tjhowse/OpenJoystick/modcon/modcon.scad

// Wall thickness
wt = 3;
// Pre-drill hole/groove depth
pd_groove_z = 1;
pd_groove_x = 1;
pd_hole_r = 1;
pd_hole_z = pd_groove_z;
// Grid spacing for the straight pre-drill grooves
pd_grid_xy = 5;
// Leave this much room around the edge without pre-drill grooves/holes.
pd_grid_clearance = 10;
// A list of radii for the circular pre-drill grooves
circles_r = [10, 20, 30];
// Overall width/height
unit_xy = 80;
unit_z = 50;
lid_screw_offset_x = wt*2;
lid_screw_shaft_r = 1.5;
lid_recess_grace = 0.4; // How much to shink the recessed part of the lid so it sockets into the base.

join_pin_x = 3*wt;
join_pin_z = join_pin_x;

// join_pin goes through the holes in the sides of the bases to lock them together.
module join_pin() {
    cube([join_pin_x+2*wt, wt, join_pin_z]);
    translate([wt,wt,0]) cube([join_pin_x, 2*wt, join_pin_z]);
    translate([wt*2,wt*3,0]) cube([wt, wt, join_pin_z]);
    translate([wt*2, wt*3,0]) rotate([0,0,90]) pin_barb();
    translate([wt*4, wt*4,0]) rotate([0,0,180]) pin_barb();

}

// join_pin_clip latches over the end of the join_pin to lock it into place
module join_pin_clip() {
    clip_scale = 1.1;
    scale([clip_scale, clip_scale, 1]) difference(){
        cube([join_pin_x+2*wt, 2*wt, join_pin_z]);
        translate([join_pin_x+2*wt, wt*5,0]) rotate([0,0,180]) join_pin();
    }
}

// pin_barb is a part of the join_pin
module pin_barb() {
    translate([wt/2, wt/2, join_pin_z/2]) difference() {
        cube([wt, wt, join_pin_z], center=true);
        rotate([0,0,45]) translate([-50,0,-join_pin_z/2]) cube([100,10,join_pin_z]);
    }
}

// spring_pin is a variant on the join_pin that uses a barbed spring arrangement
// rather than the two-piece version.
module spring_pin() {
    cube([join_pin_x+2*wt, wt, join_pin_z]);
    translate([wt,wt,0]) cube([wt/2, wt*3, join_pin_z]);
    translate([3.5*wt,wt,0]) cube([wt/2, wt*3, join_pin_z]);
    translate([0,3*wt,0]) rotate([0,0,0]) #pin_barb();
    translate([4*wt,4*wt,0]) rotate([0,0,270]) #pin_barb();
}
// spring_pin();

// join_pin_holes is for chopping the locking holes in the sides of the base
module join_pin_holes() {
    ratio = 4;
    translate([unit_xy/ratio,0,0]) cube([join_pin_z, 200, join_pin_x], center=true);
    translate([-unit_xy/ratio,0,0]) cube([join_pin_z, 200, join_pin_x], center=true);
    rotate([0,0,90]) {
        translate([unit_xy/ratio,0,0]) cube([join_pin_z, 200, join_pin_x], center=true);
        translate([-unit_xy/ratio,0,0]) cube([join_pin_z, 200, join_pin_x], center=true);
    }
}

// grid_screw is an M3x20 cup head bolt by default
module lid_screw() {
    head_r = 3;
    bolt_head_protrusion_z = 3;
    head_z = 3-bolt_head_protrusion_z;
    shaft_r = lid_screw_shaft_r;
    shaft_z = 20;
    cylinder(r=head_r, h=head_z);
    translate([0,0,head_z]) cylinder(r=shaft_r, h=shaft_z, $fn=10);
}

// base_screw_post is one of the corner screw posts for the base.
module base_screw_post() {
    difference() {
        cylinder(r=lid_screw_shaft_r+wt, h=unit_z-wt*2);
        cylinder(r=lid_screw_shaft_r, h=unit_z-wt*2, $fn=10);
    }
}

// base_screw_posts are the four posts in the corners inside the
// base. These posts provide the holes for screws that hold the lid
// on, and also add rigidity to the base by reinforcing the corners.
module base_screw_posts() {
    intersection() {
        cube([unit_xy, unit_xy, unit_z-wt/2]);
        union() {
            translate([lid_screw_offset_x, lid_screw_offset_x, wt]) base_screw_post();
            translate([unit_xy-lid_screw_offset_x, lid_screw_offset_x, wt]) base_screw_post();
            translate([unit_xy-lid_screw_offset_x, unit_xy-lid_screw_offset_x, wt]) base_screw_post();
            translate([lid_screw_offset_x, unit_xy-lid_screw_offset_x, wt]) base_screw_post();
        }
    }
}

// base is the body of the module. Basically everything except the lid.
module base() {
    difference () {
        cube([unit_xy, unit_xy, unit_z-wt/2]);
        translate([wt, wt, wt]) cube([unit_xy-2*wt, unit_xy-2*wt, unit_z]);
        translate([unit_xy/2, unit_xy/2, unit_z/2]) join_pin_holes();
    }
    base_screw_posts();
}

module lid_whole() {
    cube([unit_xy, unit_xy, wt/2]);
    translate([wt+lid_recess_grace/2,wt+lid_recess_grace/2,wt/2])
        cube([unit_xy-wt*2-lid_recess_grace, unit_xy-wt*2-lid_recess_grace, wt/2]);
}

// lid_lines is half of the straight lines in the underside of the lid
module lid_lines() {
    for (x = [pd_grid_clearance:pd_grid_xy:unit_xy-pd_grid_clearance]) {
        translate([x-pd_groove_x/2, pd_grid_clearance, 0]) cube([pd_groove_x, unit_xy-2*pd_grid_clearance, 10]);
    }
}

// lid_grid is subtracted from the lid to provide the grid
// lines to assist with drilling accurately spaced holes or
// punching out neat sections. Currently unused.
module lid_grid() {
    // lid_lines();
    // translate([unit_xy, 0, 0]) rotate([0,0,90]) lid_lines();
    for (x = [pd_grid_clearance:pd_grid_xy:unit_xy-pd_grid_clearance]) {
        for (y = [pd_grid_clearance:pd_grid_xy:unit_xy-pd_grid_clearance]) {
            translate([x, y, 0]) cylinder(r=pd_hole_r, h=10, $fn=10);
        }
    }
}

// lid_circles is subtracted from the underside of the lid
// to make it easier to punch out portions of the lid to mount
// stuff.
module lid_circles() {
    for (r = circles_r) {
        difference() {
            cylinder(r=r+pd_groove_x/2, h=10);
            cylinder(r=r-pd_groove_x/2, h=10);
        }
    }
}

// lid is the lid of a module. The grooves argument lets you turn off the grooves for improved
// rendering speed.
module lid(grooves = 1) {
    difference() {
        lid_whole();
        lsox = lid_screw_offset_x;
        translate([lsox, lsox,0]) lid_screw();
        translate([unit_xy-lsox, lsox,0]) lid_screw();
        translate([unit_xy-lsox, unit_xy-lsox,0]) lid_screw();
        translate([lsox, unit_xy-lsox,0]) lid_screw();

        if (grooves) {
            translate([unit_xy/2, unit_xy/2, wt-pd_groove_z]) lid_circles();
            translate([0, 0, wt-pd_hole_z]) lid_grid();
        }
    }
}

// lid_HW997 is a variant of the lid with the holes to mount the HW0000997 joystick
// already formed.
module lid_HW997(grooves = 1) {
    $fn=20;
    HD997_hole_r = 41/2;
    HD997_screw_spacing_xy = 32.5/2;
    HD997_screw_hole_r = 2.5/2;
    difference() {
        lid(0);
        translate([unit_xy/2, unit_xy/2,0]) {
            cylinder(r=HD997_hole_r, h=100);
            translate([HD997_screw_spacing_xy,HD997_screw_spacing_xy,0]) cylinder(r=HD997_screw_hole_r, h=100);
            translate([-HD997_screw_spacing_xy,HD997_screw_spacing_xy,0]) cylinder(r=HD997_screw_hole_r, h=100);
            translate([HD997_screw_spacing_xy,-HD997_screw_spacing_xy,0]) cylinder(r=HD997_screw_hole_r, h=100);
            translate([-HD997_screw_spacing_xy,-HD997_screw_spacing_xy,0]) cylinder(r=HD997_screw_hole_r, h=100);
        }

    }
}

10a_switch_r = 6;
10a_switch_x = 20;
10a_switch_clearance_x = 0.5;
10a_switch_y = 35;
10a_switch_z = 30;
module 10a_Switch() {
    cylinder(r=10a_switch_r, h=100);
    translate([0,0,wt+10a_switch_z/2]) cube([10a_switch_x, 10a_switch_y, 10a_switch_z], center=true);
}

// lid_6_10a_switch is a variant of the lid with holes to mount six 10A switches in a grid.
module lid_6_10a_switch(grooves = 1) {
    difference() {
        lid(0);
        translate([unit_xy/2, unit_xy/2,0]) {
            translate([0,-10a_switch_y/2,0]) 10a_Switch();
            translate([-10a_switch_x-10a_switch_clearance_x,-10a_switch_y/2,0]) 10a_Switch();
            translate([10a_switch_x+10a_switch_clearance_x,-10a_switch_y/2,0]) 10a_Switch();
            translate([0,10a_switch_y/2,0]) 10a_Switch();
            translate([-10a_switch_x-10a_switch_clearance_x,10a_switch_y/2,0]) 10a_Switch();
            translate([10a_switch_x+10a_switch_clearance_x,10a_switch_y/2,0]) 10a_Switch();
        }
    }
}

// lid(1);


module assembled() {
    base();
    translate([0,unit_xy,unit_z])
        rotate([180,0,0])
            // lid(0);
            lid_6_10a_switch(0);
}
// join_pin_clip();
// translate([20,0,0]) join_pin();

// base();
// lid(1);
// lid_HW997(0);
lid_6_10a_switch(0);
// difference() {
//     assembled();
//     translate([unit_xy/2,0,-unit_z/2]) cube([100,100,unit_z]);
// }
// intersection() {
//     base();
//     translate([0,0,17.5]) cube([unit_xy, unit_xy,join_pin_x*1.5]);
// }
